eatoin5hrdlu/PACE/CAD/cuvetteturb.PNG

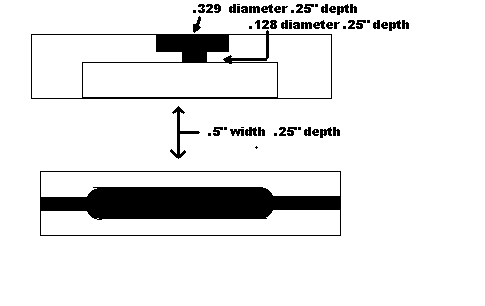
CAD/cuvetteturb.PNG
