eatoin5hrdlu/PACE/CAD/pizza.jpg

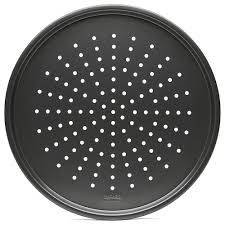
CAD/pizza.jpg
