eatoin5hrdlu/PACE/Doc/LM35DZ-Temp-Sensor.jpg

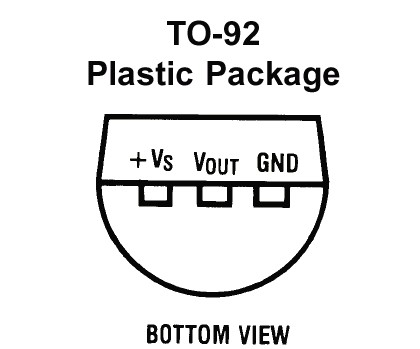
Doc/LM35DZ-Temp-Sensor.jpg
