eatoin5hrdlu/PACE/Doc/switchbox.png

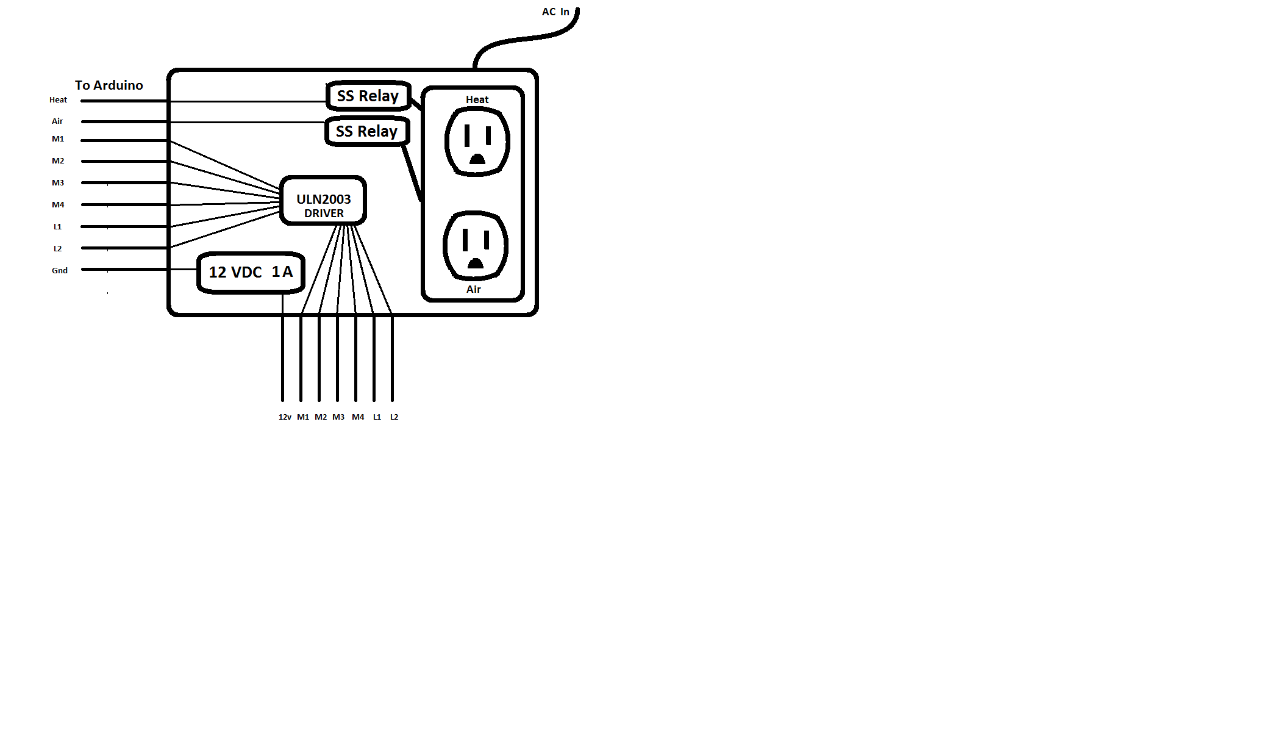
Doc/switchbox.png
