eatoin5hrdlu/PACE/open/images/biologic1.png

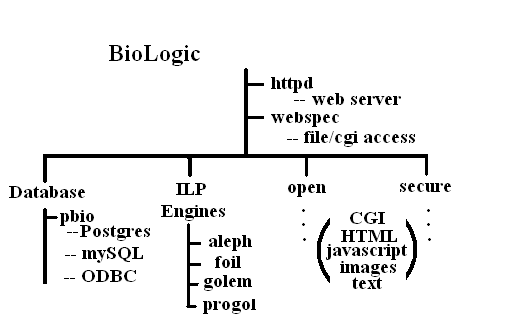
open/images/biologic1.png
