eatoin5hrdlu/PACE/open/images/biologic.png

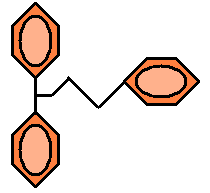
open/images/biologic.png
