eatoin5hrdlu/PACE/open/images/biologictan.png

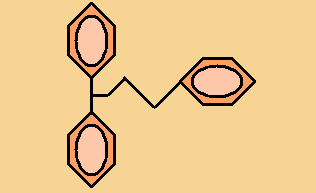
open/images/biologictan.png
