eatoin5hrdlu/PACE/open/images/evo.png

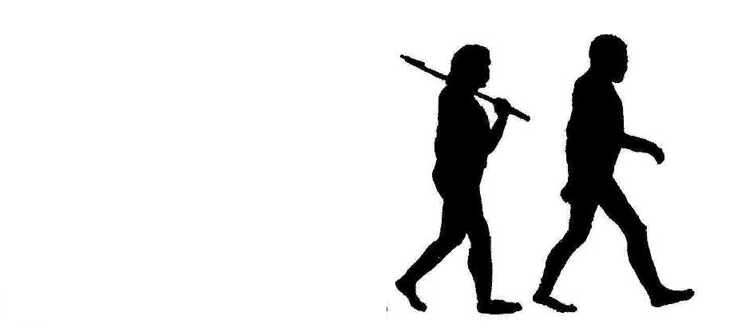
open/images/evo.png
