eatoin5hrdlu/PACE/open/images/natlang.jpg

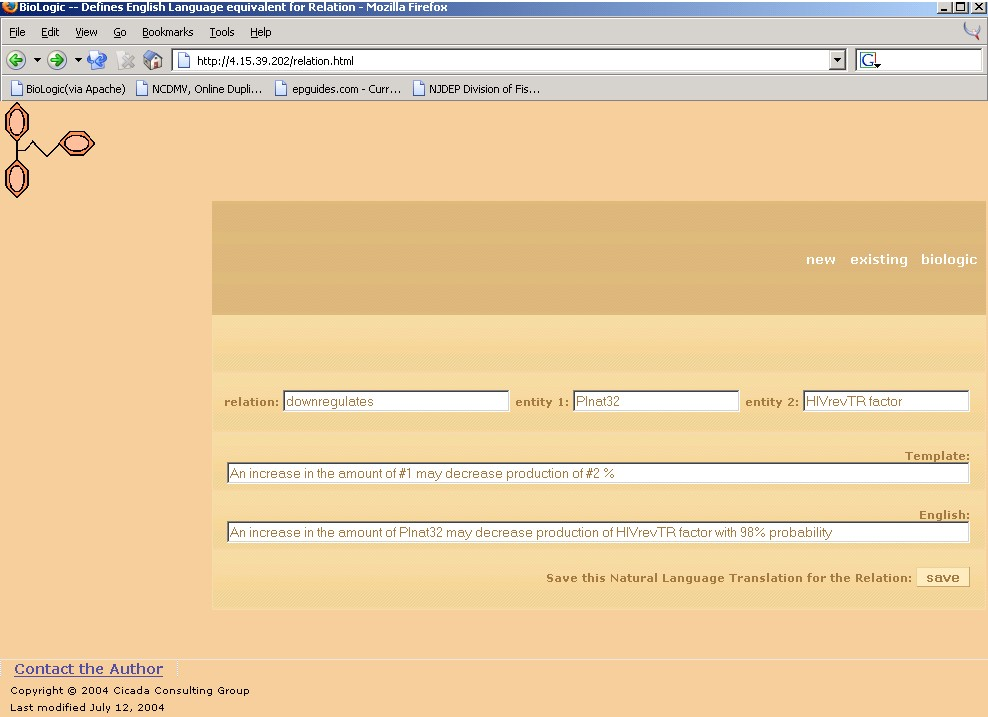
open/images/natlang.jpg
