eatoin5hrdlu/PACE/opencvlevel.jpg

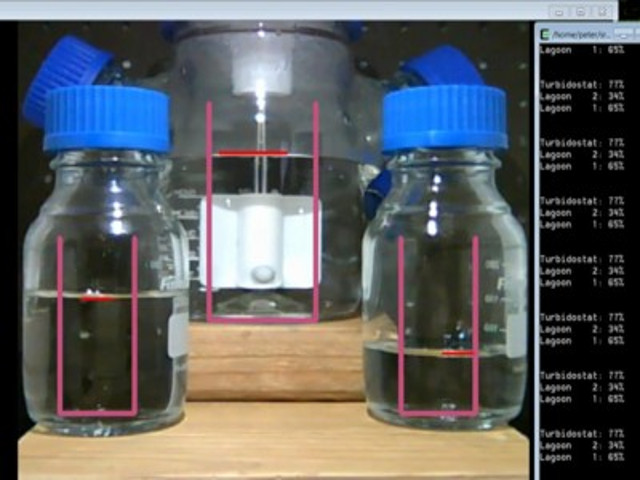
opencvlevel.jpg
