eatoin5hrdlu/PACE/phagestat.png

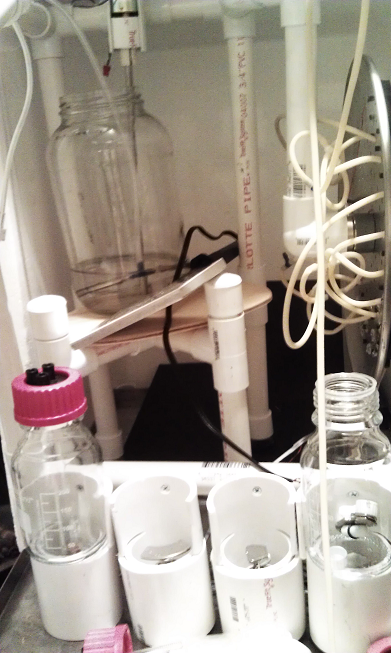
phagestat.png
