eatoin5hrdlu/PACE/tools/darkForest.png

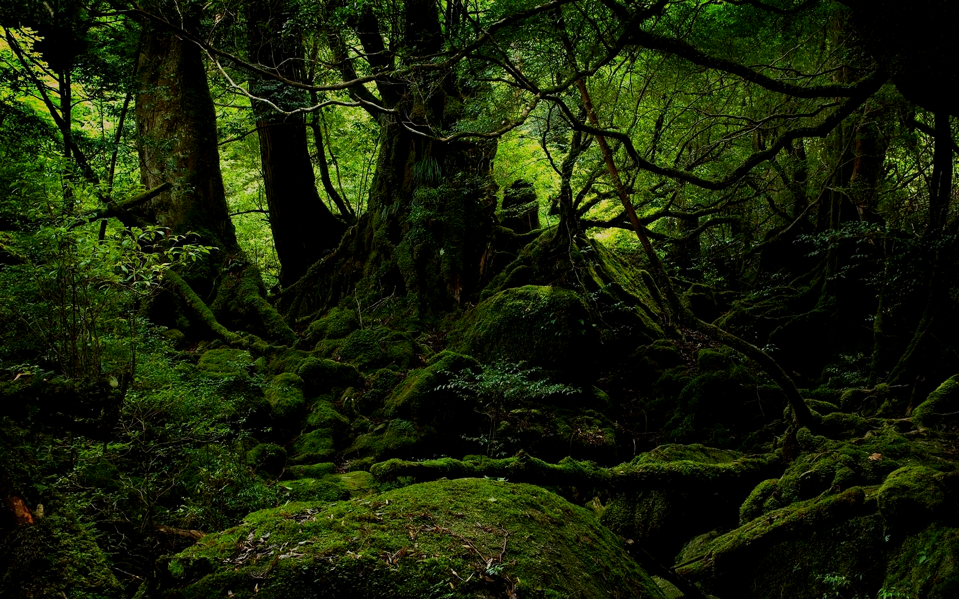
tools/darkForest.png
