eatoin5hrdlu/PACE/CAD/innatrix_logo.scad

// Module names are of the form poly_<inkscape-path-id>().  As a result,
// you can associate a polygon in this OpenSCAD program with the corresponding
// SVG element in the Inkscape document by looking for the XML element with
// the attribute id="inkscape-path-id".

// fudge value is used to ensure that subtracted solids are a tad taller
// in the z dimension than the polygon being subtracted from.  This helps
// keep the resulting .stl file manifold.
fudge = 0.1;

module innatrix_logo(h)
{
  scale([25.4/90, -25.4/90, 1]) union()
  {
    linear_extrude(height=h)
      polygon([[-214.588413,112.720586],[-216.451669,109.611419],[-217.686962,107.110512],[-218.203035,104.950527],[-217.908632,102.864126],[-216.712496,100.583973],[-214.523370,97.842728],[-206.801123,89.907616],[-201.554604,84.453452],[-197.258160,79.562834],[-194.355157,75.770489],[-193.288963,73.611146],[-193.804241,72.016446],[-195.207223,69.761494],[-197.283639,67.146216],[-199.819213,64.470536],[-202.354788,61.688527],[-204.431203,58.783736],[-205.834186,56.100308],[-206.349463,53.982386],[-205.850312,51.001992],[-204.421343,47.424524],[-202.165282,43.352512],[-199.184858,38.888485],[-191.461827,29.194509],[-182.074067,19.162836],[-171.843395,9.613708],[-161.591627,1.367365],[-156.714650,-2.010937],[-152.140581,-4.755952],[-147.972146,-6.765151],[-144.312073,-7.936004],[-136.911255,-9.899503],[-130.580483,-12.180934],[-129.132984,-12.640725],[-127.613156,-12.745992],[-126.016149,-12.494506],[-124.337115,-11.884041],[-120.713563,-9.577265],[-116.703703,-5.807844],[-112.900537,-1.368605],[-110.272327,2.546557],[-108.816593,5.916736],[-108.530852,8.721031],[-108.825954,9.904439],[-109.412625,10.938537],[-110.290554,11.820712],[-111.459430,12.548351],[-114.668787,13.529568],[-119.038213,13.861286],[-124.943880,14.296543],[-127.385946,14.887287],[-129.499556,15.768260],[-131.293754,16.970577],[-132.777581,18.525353],[-133.960079,20.463704],[-134.850291,22.816742],[-135.457258,25.615585],[-135.790024,28.891345],[-135.669116,36.998080],[-134.559907,47.385864],[-132.534733,60.303616],[-128.431230,86.154040],[-127.329621,95.379136],[-126.853371,102.431861],[-126.996426,107.532994],[-127.752735,110.903315],[-128.358968,112.008414],[-129.116245,112.763602],[-130.023809,113.196477],[-131.080903,113.334636],[-132.228570,113.130705],[-133.223060,112.510789],[-134.068860,111.462707],[-134.770460,109.974279],[-135.759006,105.627655],[-136.224603,99.373466],[-136.945707,92.988681],[-138.601078,85.924926],[-140.944462,79.041142],[-143.729603,73.196266],[-150.817913,60.980236],[-150.866013,71.451116],[-151.471962,82.542590],[-152.861323,94.505526],[-153.623071,101.088257],[-153.587540,103.398380],[-153.230468,105.183540],[-152.518902,106.540635],[-151.419886,107.566564],[-149.900468,108.358225],[-147.927693,109.012516],[-144.658996,110.242855],[-142.489348,111.710287],[-141.384063,113.291174],[-141.308456,114.861876],[-142.227839,116.298756],[-144.107525,117.478175],[-146.912829,118.276495],[-150.609063,118.570076],[-155.090328,118.215685],[-158.995062,117.126523],[-162.356083,115.263608],[-165.206211,112.587956],[-167.578263,109.060586],[-169.505058,104.642514],[-171.019416,99.294759],[-172.154153,92.978336],[-174.263683,77.940866],[-183.942553,87.605796],[-188.202837,91.528876],[-192.647682,95.065899],[-196.750683,97.828888],[-199.985433,99.429866],[-202.495715,100.663964],[-204.371071,102.352982],[-205.596536,104.350082],[-206.157146,106.508431],[-206.037936,108.681193],[-205.223942,110.721533],[-203.700200,112.482616],[-201.451743,113.817606],[-199.219057,114.986170],[-197.697683,116.302182],[-196.873369,117.672171],[-196.731860,119.002670],[-197.258901,120.200208],[-198.440238,121.171316],[-200.261617,121.822526],[-202.708783,122.060366],[-204.061984,121.869740],[-205.550277,121.323399],[-208.737241,119.316806],[-211.879876,116.347048],[-214.588383,112.720586]]);
    difference()
    {
       linear_extrude(height=h)
         polygon([[53.469817,118.744216],[52.093228,118.031053],[50.808590,117.011232],[48.584352,114.168790],[46.935468,110.451246],[46.000307,106.092956],[44.167720,95.546606],[41.420187,84.527636],[40.269942,79.293227],[39.650820,73.435514],[39.603842,67.670279],[40.170027,62.713306],[40.833928,58.652350],[41.053008,55.326779],[40.827647,53.079771],[40.548420,52.467972],[40.158227,52.254506],[37.629732,54.034110],[32.342470,58.879567],[16.585557,74.807906],[4.381335,87.906126],[0.784031,92.245147],[-1.387301,95.586055],[-2.315584,98.285309],[-2.183741,100.699369],[-1.174696,103.184695],[0.528627,106.097746],[4.087120,112.281823],[5.590724,116.098600],[5.599348,117.270800],[5.127134,118.033033],[4.185047,118.445919],[2.784047,118.570076],[0.894741,117.652604],[-2.135961,115.206315],[-9.897358,107.564041],[-17.051751,99.316773],[-19.323697,96.114239],[-20.150743,94.138026],[-18.707898,91.840503],[-14.821023,86.874940],[-2.086163,71.863266],[4.906177,63.303788],[10.468024,55.170612],[14.616898,47.401379],[16.166945,43.633754],[17.370319,39.933729],[18.229210,36.293510],[18.745807,32.705301],[18.922301,29.161309],[18.760883,25.653737],[18.263741,22.174790],[17.433066,18.716675],[16.271048,15.271595],[14.779877,11.831756],[13.431879,8.642883],[12.422907,5.222461],[11.742264,1.305487],[11.379255,-3.373044],[11.563360,-16.074791],[12.889657,-35.002814],[14.307522,-49.710628],[15.942310,-62.665195],[17.591767,-72.465207],[19.053637,-77.709357],[19.784448,-79.531374],[19.906586,-81.229567],[19.311904,-82.911237],[17.892253,-84.683683],[15.539484,-86.654205],[12.145449,-88.930103],[1.800987,-94.827227],[-5.796863,-99.240681],[-11.399472,-103.082033],[-14.472562,-105.938789],[-14.893575,-106.869039],[-14.481853,-107.398456],[-13.359398,-107.517816],[-11.743432,-107.272833],[-7.335137,-105.813207],[-1.865298,-103.266314],[4.057757,-99.878889],[14.595485,-93.751684],[18.325140,-92.080893],[21.158424,-91.322174],[23.192667,-91.463176],[24.525197,-92.491548],[25.253340,-94.394938],[25.474427,-97.160994],[25.643188,-99.848104],[26.132529,-102.400359],[26.917035,-104.801209],[27.971290,-107.034101],[30.787388,-110.929809],[34.377503,-113.955075],[38.538314,-115.977487],[40.769193,-116.571246],[43.066500,-116.864638],[45.404821,-116.841112],[47.758741,-116.484117],[50.102845,-115.777101],[52.411717,-114.703514],[53.690313,-113.726553],[54.811331,-112.332371],[56.575560,-108.507687],[57.694255,-103.660136],[58.157267,-98.220395],[57.954445,-92.619141],[57.075640,-87.287051],[55.510704,-82.654800],[54.467765,-80.735701],[53.249487,-79.153065],[50.978901,-76.314088],[50.633137,-75.277989],[50.866830,-74.419377],[51.719807,-73.679671],[53.231896,-73.000294],[58.392717,-71.588203],[62.993598,-70.144015],[68.138637,-67.937733],[73.474307,-65.192788],[78.647084,-62.132615],[83.303442,-58.980645],[87.089855,-55.960311],[89.652798,-53.295047],[90.364992,-52.165388],[90.638747,-51.208284],[90.241536,-50.234457],[89.057870,-49.794089],[87.270701,-49.907325],[85.062977,-50.594314],[78.907101,-52.811241],[76.778449,-53.090998],[75.105468,-52.735812],[73.755271,-51.683829],[72.594969,-49.873195],[70.312497,-43.728554],[68.573111,-38.974390],[66.293294,-33.770309],[63.768906,-28.746198],[61.295807,-24.531944],[58.305042,-19.346526],[55.826365,-13.771370],[53.871319,-7.869546],[52.451442,-1.704124],[51.578275,4.661828],[51.263360,11.165240],[51.518237,17.743042],[52.354447,24.332166],[56.570334,50.555955],[59.204059,71.074982],[60.282040,86.142539],[60.245883,91.711170],[59.830697,96.011916],[59.139527,101.860617],[59.312359,103.771097],[59.941003,105.148602],[61.108107,106.100337],[62.896323,106.733505],[68.666687,107.472956],[72.287350,107.958810],[75.676865,108.766006],[78.707896,109.821605],[81.253107,111.052665],[83.185160,112.386248],[84.376721,113.749414],[84.700452,115.069223],[84.029017,116.272736],[82.026203,117.330847],[78.708479,118.239264],[69.719783,119.478302],[60.245891,119.732428],[56.321673,119.409703],[53.469767,118.744216]]);
       translate([0, 0, -fudge])
         linear_extrude(height=h+2*fudge)
           polygon([[61.253747,-59.708750],[59.815555,-61.873570],[57.799273,-64.030718],[55.480203,-66.010158],[53.133645,-67.641851],[51.034903,-68.755760],[49.459276,-69.181846],[48.953663,-69.083820],[48.682067,-68.750073],[48.978577,-67.290403],[54.382838,-55.774102],[57.817615,-49.662745],[59.026966,-48.313185],[60.020568,-47.929979],[60.890629,-48.384833],[61.729357,-49.549454],[62.456287,-51.673309],[62.608924,-54.296711],[62.202875,-57.086308],[61.253747,-59.708750]]);
    }
    linear_extrude(height=h)
      polygon([[97.886767,116.426926],[93.706576,114.093351],[90.619274,111.595809],[88.872226,109.185428],[88.578599,108.091400],[88.712797,107.113336],[95.570927,85.056626],[98.220556,77.502845],[101.602957,70.099231],[105.283189,63.696057],[108.826317,59.143596],[112.558655,54.671712],[113.954351,52.323886],[115.058728,49.842104],[115.888534,47.181842],[116.460517,44.298574],[116.898007,37.684926],[116.616492,32.432483],[115.843472,28.194257],[114.686234,25.363177],[113.997061,24.598105],[113.252067,24.332166],[112.473343,24.198558],[111.868606,23.803964],[111.187150,22.269197],[111.219820,19.802625],[111.978737,16.479006],[112.965463,11.364226],[113.898178,3.243159],[114.671797,-6.767575],[115.181237,-17.551354],[115.776436,-31.707458],[116.614836,-44.193267],[117.702556,-55.043937],[119.045715,-64.294626],[120.650433,-71.980489],[122.522828,-78.136684],[124.669019,-82.798369],[127.095127,-86.000699],[129.537639,-89.192167],[131.479322,-93.366275],[132.761034,-98.084027],[133.223637,-102.906427],[133.532804,-107.499083],[134.374594,-111.889272],[135.620444,-115.579380],[137.141787,-118.071794],[139.020903,-119.728824],[141.089208,-120.930658],[143.303702,-121.700203],[145.621384,-122.060366],[147.999254,-122.034054],[150.394313,-121.644175],[152.763562,-120.913634],[155.063999,-119.865340],[157.252626,-118.522199],[159.286442,-116.907119],[161.122448,-115.043007],[162.717644,-112.952769],[164.029029,-110.659313],[165.013605,-108.185545],[165.628370,-105.554374],[165.830327,-102.788706],[165.628460,-98.282024],[165.107759,-94.079804],[164.303214,-90.273411],[163.249813,-86.954210],[161.982544,-84.213566],[160.536396,-82.142844],[158.946357,-80.833410],[157.247417,-80.376629],[155.084139,-79.986203],[154.561267,-79.403231],[154.414029,-78.477364],[155.255818,-75.343769],[157.628237,-70.079077],[159.562466,-65.149341],[161.146438,-59.339079],[162.216691,-53.373491],[162.609767,-47.977774],[162.971452,-41.629200],[163.549540,-39.366369],[164.504439,-37.556019],[165.920138,-36.081779],[167.880622,-34.827280],[173.771897,-32.512034],[178.841916,-31.134601],[182.943702,-30.643378],[186.061720,-31.038569],[187.246962,-31.568636],[188.180437,-32.320384],[189.922035,-33.698465],[191.685079,-34.273804],[193.355239,-34.136492],[194.818185,-33.376620],[195.959587,-32.084281],[196.665115,-30.349565],[196.820438,-28.262566],[196.311227,-25.913374],[196.065841,-24.627840],[196.111920,-23.030936],[196.995785,-19.156549],[198.797439,-14.797271],[201.351497,-10.460164],[204.627299,-5.475577],[206.754627,-1.521227],[207.672681,1.515580],[207.659232,2.725120],[207.320664,3.747535],[206.649379,4.596910],[205.637777,5.287332],[202.563220,6.247663],[198.036196,6.741220],[191.995907,6.880696],[186.332652,6.760050],[181.990574,6.337682],[178.889621,5.522946],[176.949743,4.225196],[176.390190,3.366864],[176.090887,2.353786],[176.233001,-0.181930],[177.296035,-3.472598],[179.199937,-7.608864],[181.421196,-12.530172],[181.676756,-14.148355],[181.226708,-15.380296],[179.969381,-16.357550],[177.803104,-17.211670],[170.337017,-19.076724],[164.694351,-20.035161],[162.718031,-19.915723],[161.144594,-19.295328],[159.853694,-18.097585],[158.724986,-16.246107],[156.472767,-10.276384],[155.370062,-6.029058],[155.001355,-1.890984],[155.474395,2.421857],[156.896935,7.193482],[159.376726,12.707910],[163.021517,19.249158],[167.939060,27.101244],[174.237107,36.548186],[177.168666,41.811260],[179.891908,48.400986],[182.102962,55.475850],[183.497957,62.194336],[184.697844,69.023583],[186.377717,76.400007],[188.314824,83.436039],[190.286417,89.244106],[193.108688,95.463812],[194.537140,97.547436],[196.132797,99.060751],[198.012401,100.089143],[200.292698,100.717995],[206.522347,101.118616],[211.642029,101.507097],[215.294750,102.557981],[217.481442,104.099432],[218.025318,105.000420],[218.203035,105.959610],[218.014711,106.955523],[217.460462,107.966679],[215.254651,109.948802],[211.586536,111.734140],[206.457047,113.150856],[196.964214,115.318299],[190.514387,117.245906],[189.385904,117.074154],[187.895274,115.879662],[184.067633,110.912147],[179.511589,103.322735],[174.707270,94.090797],[170.134802,84.195709],[166.274311,74.616842],[163.605924,66.333570],[162.868809,62.983837],[162.609767,60.325266],[162.386646,58.550972],[161.747175,56.406842],[159.398534,51.336614],[155.922542,45.769656],[151.677897,40.361046],[140.746027,27.970546],[136.616007,42.730246],[134.196909,49.427104],[130.663315,56.750264],[126.489858,63.813747],[122.151167,69.731576],[117.778012,75.414752],[113.510703,81.839327],[109.838198,88.216903],[107.249457,93.759076],[104.953610,100.262425],[104.442574,102.568040],[104.373648,104.432176],[104.759968,105.996755],[105.614673,107.403698],[108.781787,110.312356],[111.487210,112.163461],[114.344734,113.679355],[117.013997,114.703607],[119.154637,115.079786],[120.814003,115.355192],[122.172880,116.105059],[123.091041,117.214862],[123.428257,118.570076],[123.282341,119.421184],[122.856899,120.133723],[121.241269,121.149292],[118.729026,121.629174],[115.467832,121.585757],[111.605347,121.031434],[107.289234,119.978595],[102.667154,118.439628],[97.886767,116.426926]]);
    linear_extrude(height=h)
      polygon([[-102.681713,114.800216],[-104.549821,113.286669],[-106.052415,111.352998],[-107.202871,109.070646],[-108.014564,106.511057],[-108.500868,103.745674],[-108.675159,100.845941],[-108.141202,94.929195],[-106.519692,89.332367],[-105.334542,86.832530],[-103.917629,84.627003],[-102.282327,82.787229],[-100.442012,81.384651],[-98.410059,80.490712],[-96.199843,80.176856],[-93.891278,79.745518],[-90.828298,78.571082],[-87.410044,76.832919],[-84.035653,74.710396],[-76.231003,69.243946],[-84.443803,51.765016],[-87.804431,43.789911],[-90.006815,36.703370],[-90.998100,30.721659],[-91.023064,28.212699],[-90.725433,26.061046],[-90.234059,22.140723],[-90.323750,17.546790],[-90.950390,12.851320],[-92.069863,8.626386],[-92.903527,5.926542],[-93.376479,3.394324],[-93.462616,0.901105],[-93.135837,-1.681743],[-92.370040,-4.482845],[-91.139121,-7.630830],[-87.177513,-15.481954],[-84.006047,-21.718265],[-81.408891,-27.684694],[-79.654056,-32.704660],[-79.009553,-36.101584],[-78.378442,-38.764936],[-76.660070,-41.787569],[-74.116879,-44.797946],[-71.011313,-47.424534],[-67.375736,-50.559953],[-63.389443,-54.955775],[-59.535278,-60.028870],[-56.296083,-65.196105],[-53.227400,-69.974832],[-50.044267,-73.410778],[-46.756590,-75.503718],[-45.076644,-76.046489],[-43.374277,-76.253425],[-41.650728,-76.124495],[-39.907234,-75.659674],[-36.365368,-73.722239],[-32.758586,-70.440896],[-29.096793,-65.815419],[-26.449986,-61.434881],[-24.870814,-57.484646],[-24.341306,-54.012109],[-24.843492,-51.064664],[-26.359402,-48.689706],[-28.871066,-46.934629],[-32.360513,-45.846827],[-36.809773,-45.473694],[-41.900549,-45.231588],[-43.551477,-44.876590],[-44.665887,-44.319079],[-45.288621,-43.524144],[-45.464521,-42.456874],[-44.655183,-39.365684],[-42.484096,-32.707059],[-40.636963,-25.275244],[-40.020608,-23.457245],[-38.881815,-21.346566],[-35.297868,-16.550548],[-30.407032,-11.493947],[-24.731213,-6.783524],[-20.016984,-2.973104],[-16.187991,0.835636],[-13.278664,4.561635],[-11.323435,8.123827],[-10.356732,11.441152],[-10.412985,14.432543],[-11.526626,17.016939],[-13.732083,19.113276],[-15.354069,19.537224],[-17.329169,19.084727],[-19.481890,17.918119],[-21.636738,16.199737],[-23.618221,14.091917],[-25.250843,11.756993],[-26.359112,9.357301],[-26.767533,7.055176],[-26.946475,5.982133],[-27.456018,4.898188],[-29.303213,2.768698],[-31.981732,0.808920],[-35.164188,-0.838930],[-38.523195,-2.032639],[-41.731364,-2.629992],[-44.461309,-2.488775],[-45.544639,-2.096761],[-46.385643,-1.466774],[-47.740937,0.643884],[-49.128140,3.928945],[-50.384454,7.939142],[-51.347083,12.225206],[-51.750682,15.240951],[-51.789708,18.001007],[-51.410123,20.636738],[-50.557893,23.279505],[-49.178981,26.060671],[-47.219351,29.111598],[-41.341793,36.548186],[-37.212687,41.693059],[-34.154289,46.429840],[-32.115466,51.256483],[-31.045087,56.670944],[-30.892019,63.171177],[-31.605131,71.255137],[-33.133289,81.420778],[-35.425363,94.166056],[-35.985051,99.303125],[-35.715932,101.220885],[-34.993917,102.839412],[-33.753815,104.259671],[-31.930434,105.582622],[-26.273073,108.340456],[-15.339593,112.994736],[-29.556223,114.255696],[-35.242689,114.567192],[-40.216238,114.483180],[-43.941188,114.036354],[-45.881853,113.259406],[-46.713246,110.333474],[-47.417897,104.035464],[-47.921404,95.291699],[-48.149363,85.028506],[-48.492702,70.799787],[-48.953248,65.765202],[-49.705836,61.724999],[-50.825058,58.385077],[-52.385509,55.451337],[-54.461779,52.629676],[-57.128463,49.625996],[-60.390357,46.362213],[-62.880109,44.412147],[-64.616052,43.819524],[-65.207073,44.045918],[-65.616517,44.628069],[-65.899838,46.881506],[-65.484346,50.623562],[-62.630253,62.748426],[-61.124749,69.332060],[-60.904492,71.789768],[-61.072573,73.864761],[-61.653996,75.687061],[-62.673766,77.386687],[-66.128363,80.937996],[-69.675848,83.446962],[-74.295558,85.845436],[-79.389306,87.861553],[-84.358903,89.223446],[-90.830508,90.775208],[-92.771278,91.713752],[-93.985677,92.994342],[-94.576441,94.792180],[-94.646307,97.282467],[-93.634293,105.041196],[-92.989656,109.738626],[-92.753204,113.335555],[-92.974499,115.885441],[-93.703097,117.441740],[-94.988559,118.057910],[-96.880443,117.787408],[-99.428308,116.683691],[-102.681713,114.800216]]);
  }
}
