eatoin5hrdlu/PACE/pump/param.h

#define STANDALONE 1

#define SAVE	1          // EEPROM STORAGE COMMANDS
#define RESTORE	0

#define MAX_VALVES      6
#define MAX_PUMPS       6

#define NUTRIENT_PUMP    2
#define NUTRIENT_VALVE   3

#define CELLSTAT_PUMP    4
#define CELLSTAT_VALVE   5

#define INDUCER1_PUMP    6
#define INDUCER1_VALVE   7

#define INDUCER2_PUMP    8
#define INDUCER2_VALVE  10

#define INHIBITOR_PUMP  11
#define INHIBITOR_VALVE 12

#define HEATER 13         // Nutrient heater? not PWM  NYI
#define MIXER  9          // Nutrient Mixer? PWM   NYI
#define MIXERSPEED 180   // PWM value for top nutrient mixer speed
