eatoin5hrdlu/PACE/lagoon3/param.h

#define STANDALONE 1

#define SAVE	1          // EEPROM STORAGE COMMANDS
#define RESTORE	0

#define ANALOG_TEMPERATURE   0 // Analog input for temperature

#define NUM_VALVES      4

#define LAGOONOUT       2
#define VALVEENABLE     8
#define VALVEPIN        9

#define LED            10     // Meniscus light
#define HEATER         11
#define MIXER           3     // PWM for 12V motor

#define MIXERSPEED 50   // PWM value for top mixer speed

#define DEFAULT_CYCLETIME 30 // This can be changed remembered(EEPROM)
