eatoin5hrdlu/PACE/lagoon2/param.h

#define STANDALONE 1

#define SAVE	1          // EEPROM STORAGE COMMANDS
#define RESTORE	0

#define ANALOG_TEMPERATURE   0 // Analog input for temperature

#define NUM_VALVES      4

#define LAGOONOUT       2
#define HOSTCELLS       4
#define INDUCER1        5
#define INDUCER2        6
#define INHIBIT1        7
#define INHIBIT2        8

#define LED            10     // Meniscus light
#define HEATER         11
#define MIXER           3     // PWM for 12V motor

#define MIXERSPEED 180   // PWM value for top mixer speed

#define DEFAULT_CYCLETIME 60 // This can be changed remembered(EEPROM)

#define VPOS1        0
#define VPOS2       60
#define VPOS3       110
#define VPOS4       159
#define VPOS        180
