eatoin5hrdlu/PACE/drain/param.h

#define STANDALONE 1

#define SAVE	1          // EEPROM STORAGE COMMANDS
#define RESTORE	0

#define DEFAULT_CYCLETIME  60

#define MAX_VALVES       6

#define LAGOON1_DRAIN    3
#define LAGOON2_DRAIN    4
#define LAGOON3_DRAIN    5
#define LAGOON4_DRAIN    6
#define CELLSTAT_DRAIN   7
